cgarcia2097/8-Pack/case/views/OSH Park/Rev-1.2/Bottom.png

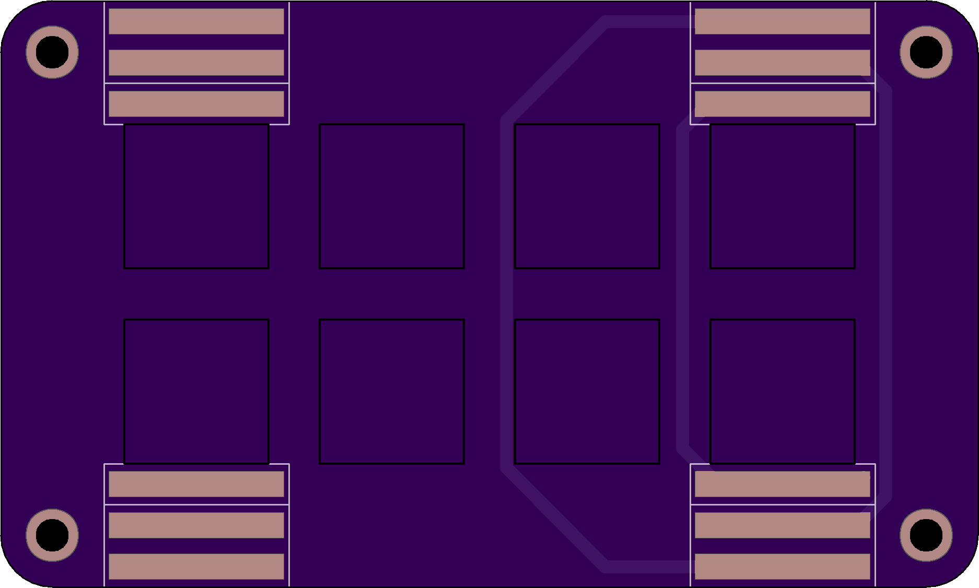
case/views/OSH Park/Rev-1.2/Bottom.png
