cgarcia2097/8-Pack/images/programming/getcode.PNG

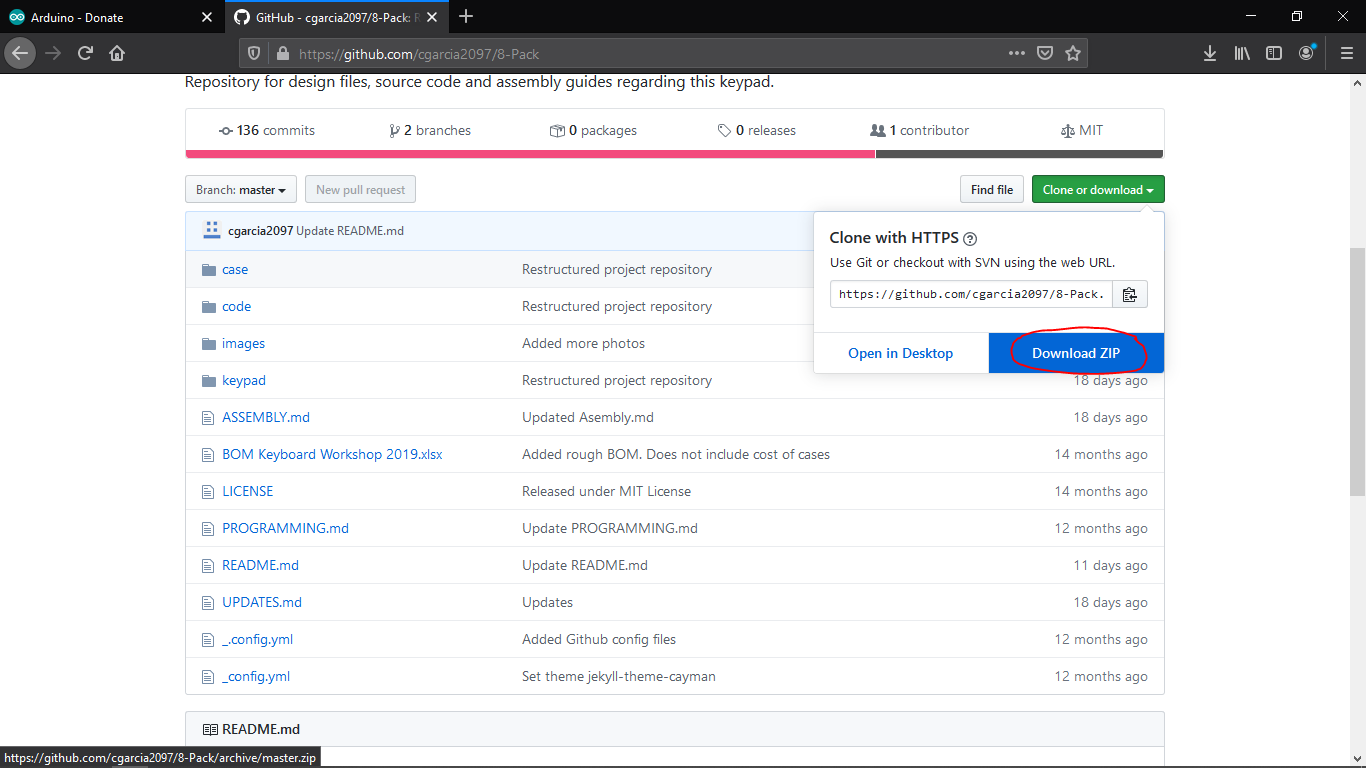
images/programming/getcode.PNG
