cgarcia2097/8-Pack/images/programming/gotolib.PNG

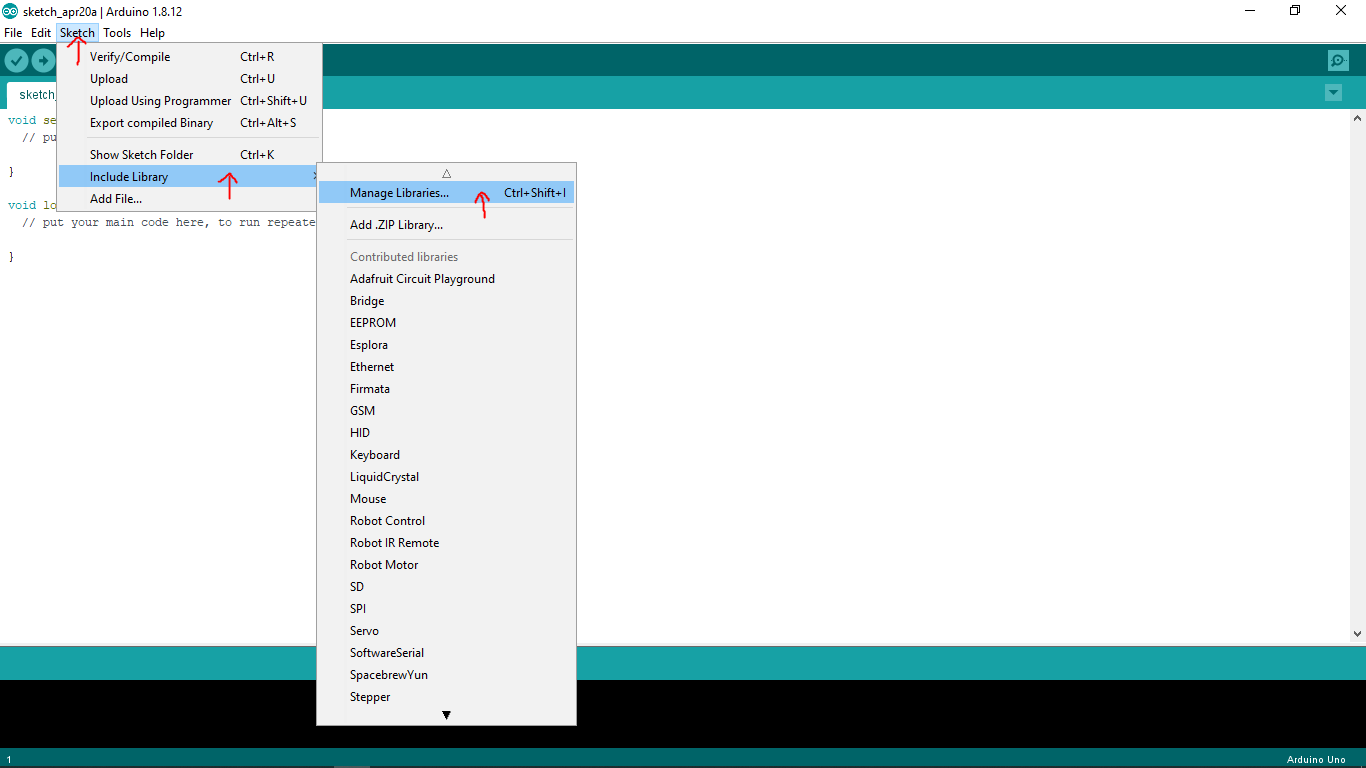
images/programming/gotolib.PNG
