cgarcia2097/8-Pack/keypad/8keysimple/views/KiCAD/back.png

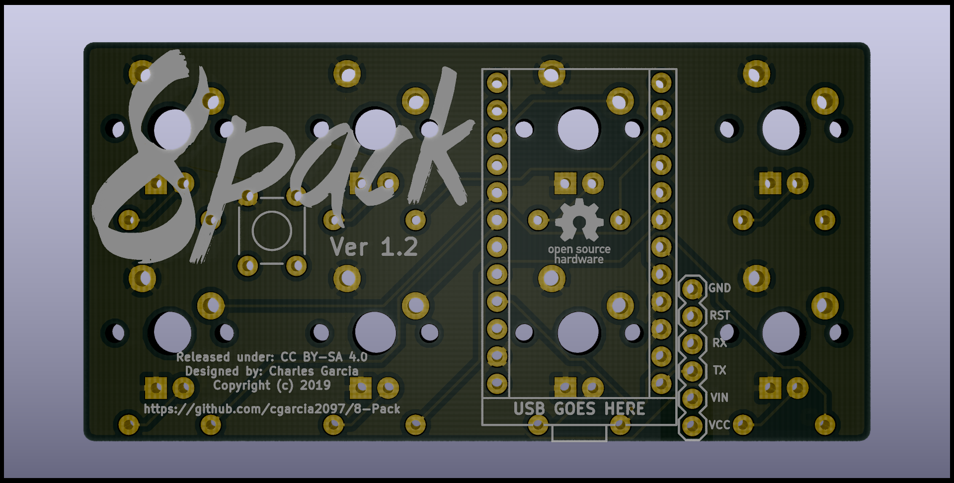
keypad/8keysimple/views/KiCAD/back.png
