cgarcia2097/8-Pack/keypad/8keysimple/views/KiCAD/front.png

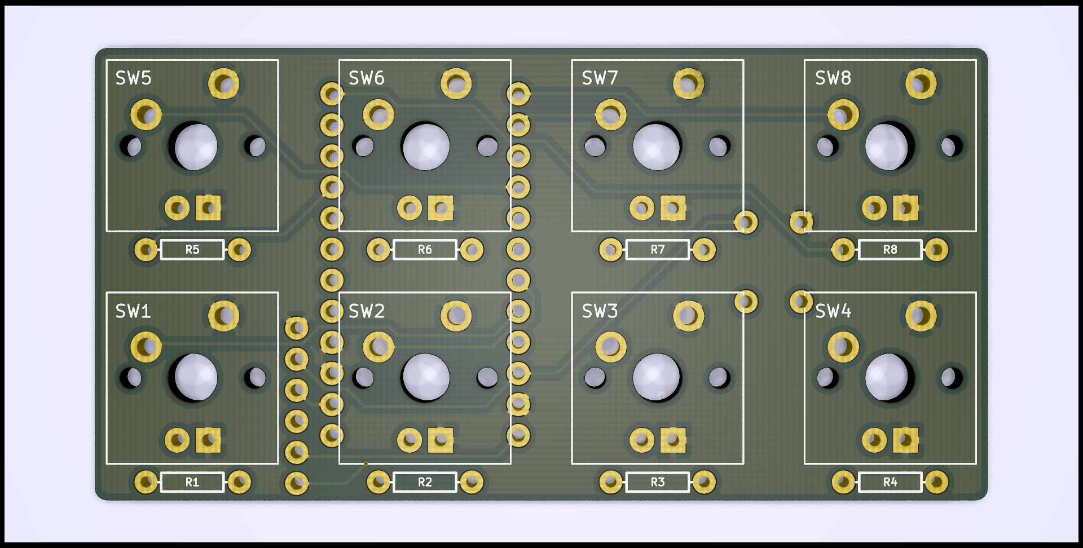
keypad/8keysimple/views/KiCAD/front.png
