cgarcia2097/8-Pack/keypad/8keysimple/views/OSH Park/1.2.1/back.png

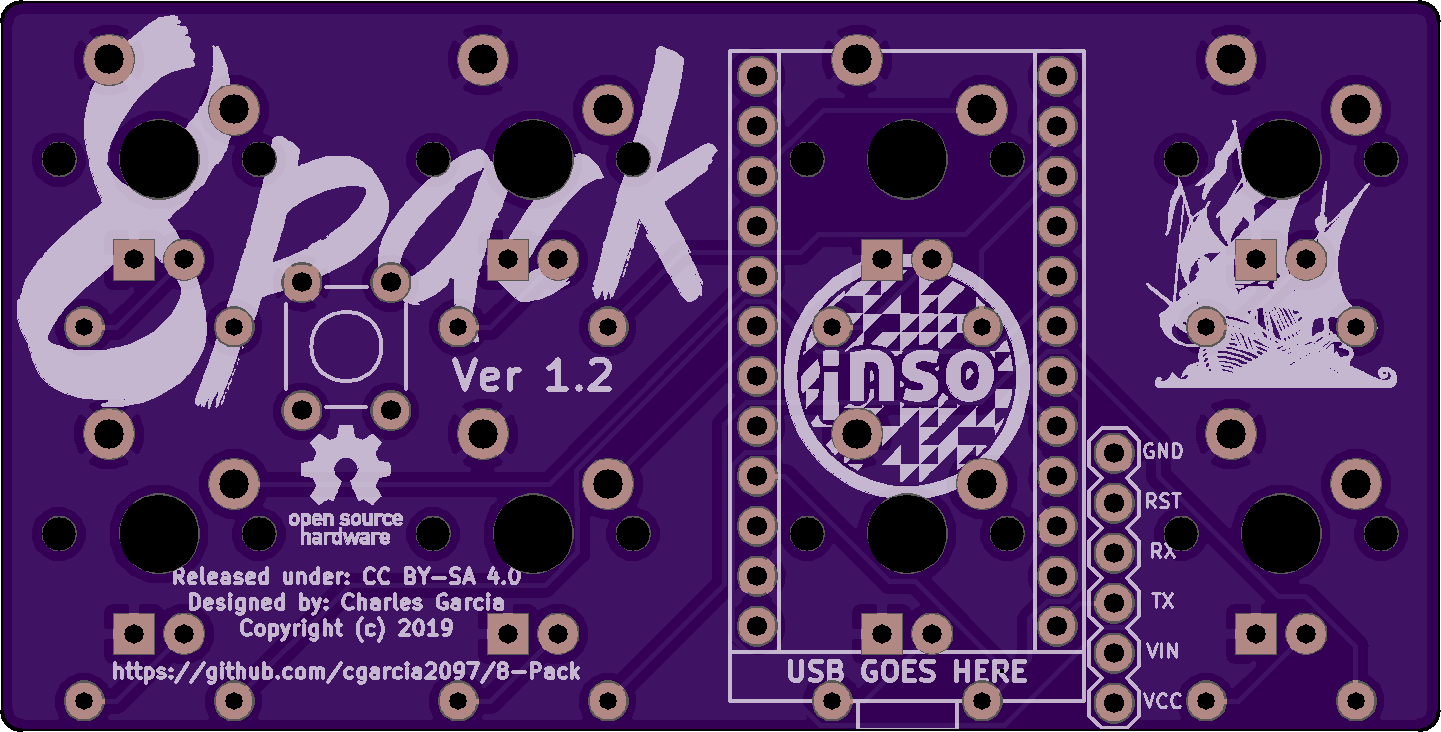
keypad/8keysimple/views/OSH Park/1.2.1/back.png
