cgarcia2097/8-Pack/keypad/8keysimple/views/x2/back.png

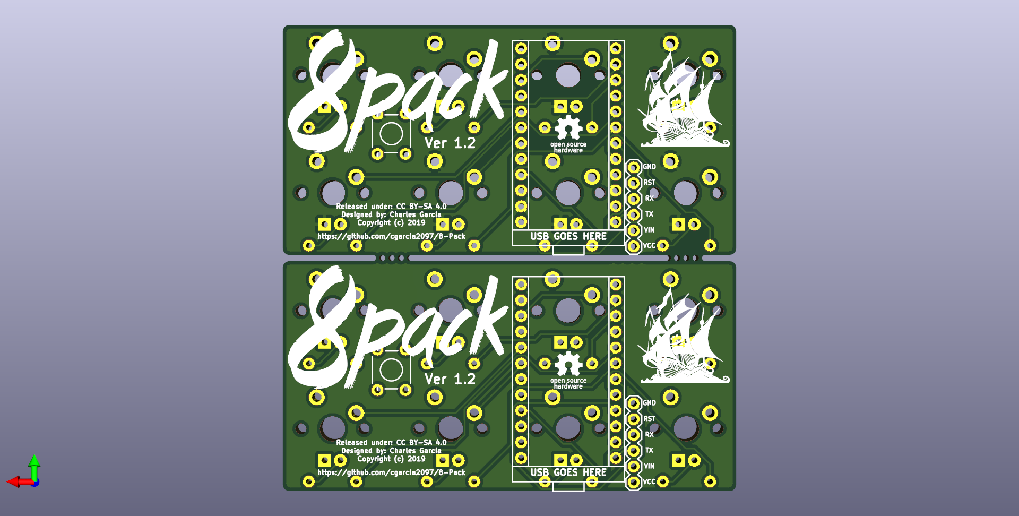
keypad/8keysimple/views/x2/back.png
