cgarcia2097/8-Pack/keypad/8keysimplev5/views/OSH Park/1.4.0/bottom.png

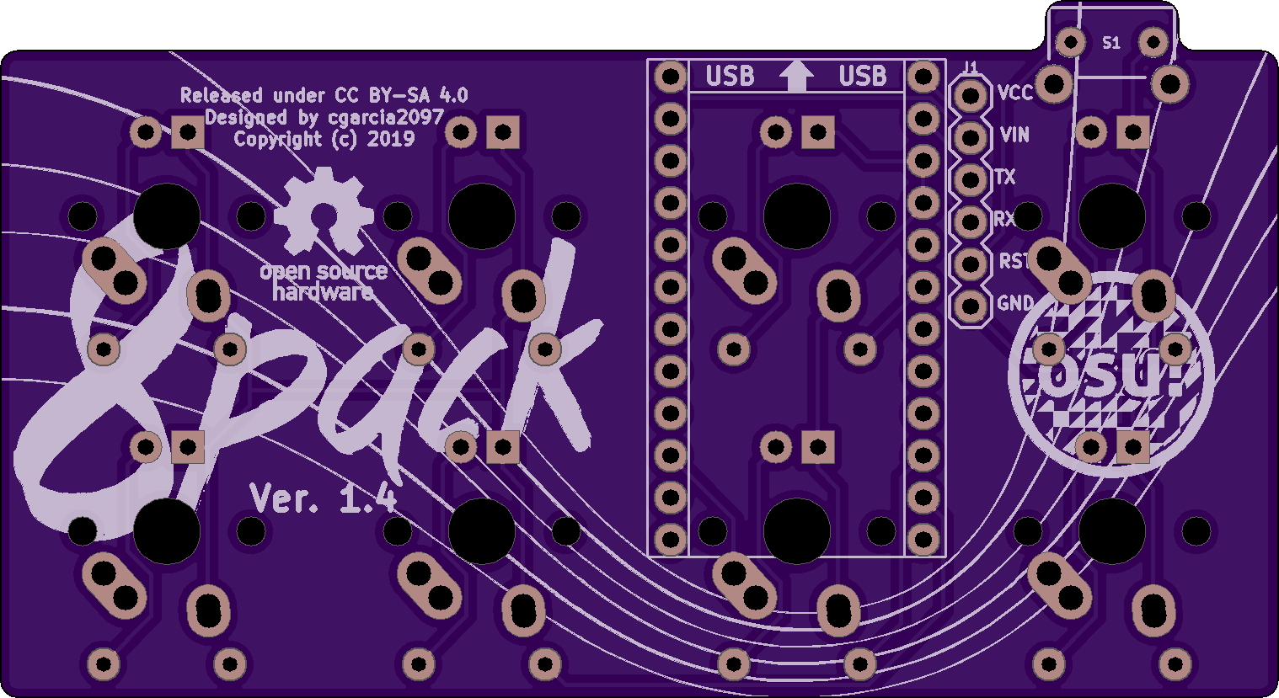
keypad/8keysimplev5/views/OSH Park/1.4.0/bottom.png
