cgarcia2097/8-Pack/keypad/8keysimplev6/views/OSH Park/pcb_osu_ontario_top.png

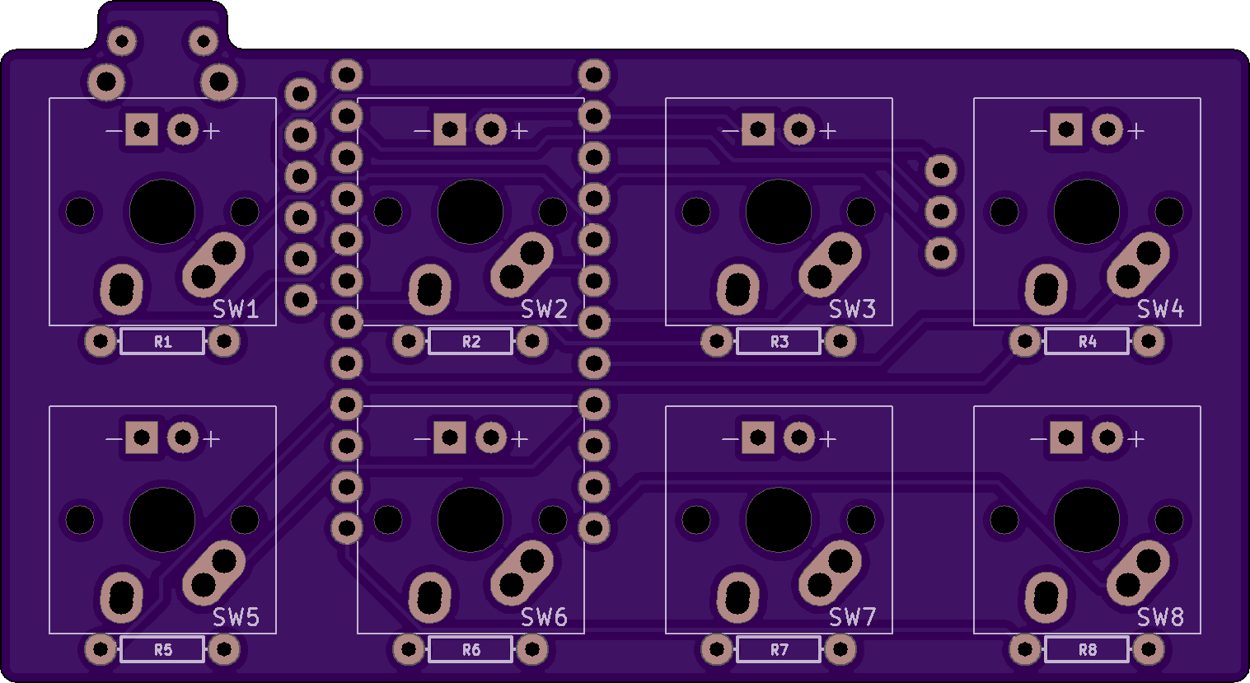
keypad/8keysimplev6/views/OSH Park/pcb_osu_ontario_top.png
