cgarcia2097/8-Pack/keypad/8keysimplev6/views/OSH Park/pcb_simple_bottom.png

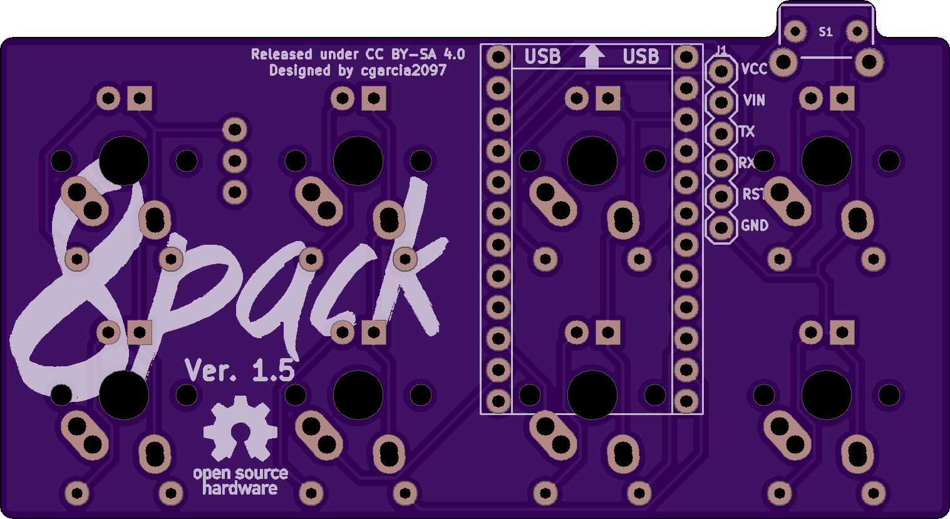
keypad/8keysimplev6/views/OSH Park/pcb_simple_bottom.png
