cgarcia2097/8-Pack/images/assembly/IMG_0136.JPG

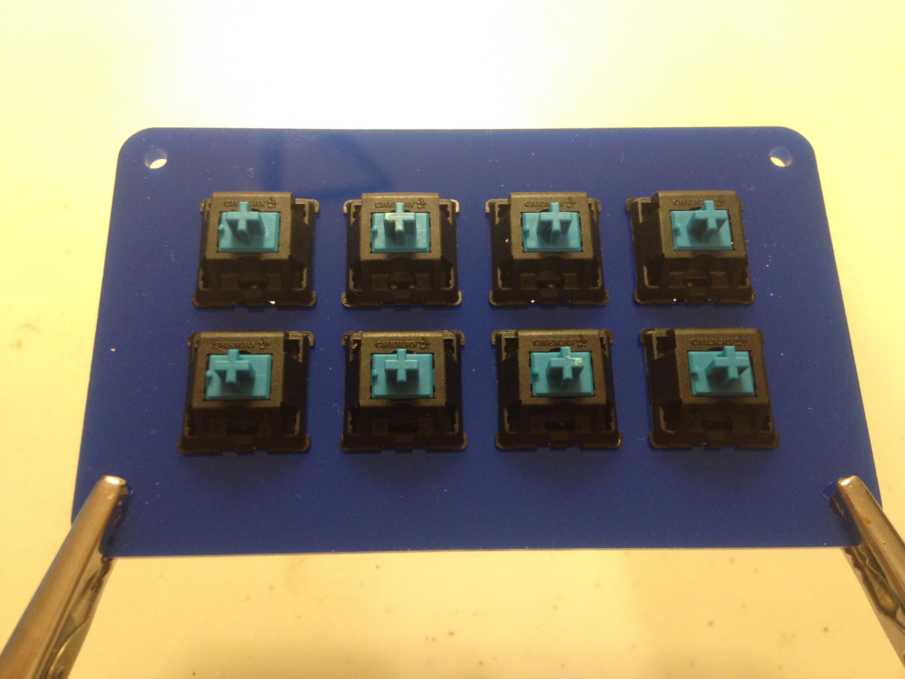
images/assembly/IMG_0136.JPG
