cgarcia2097/8-Pack/images/assembly/IMG_2523.JPG

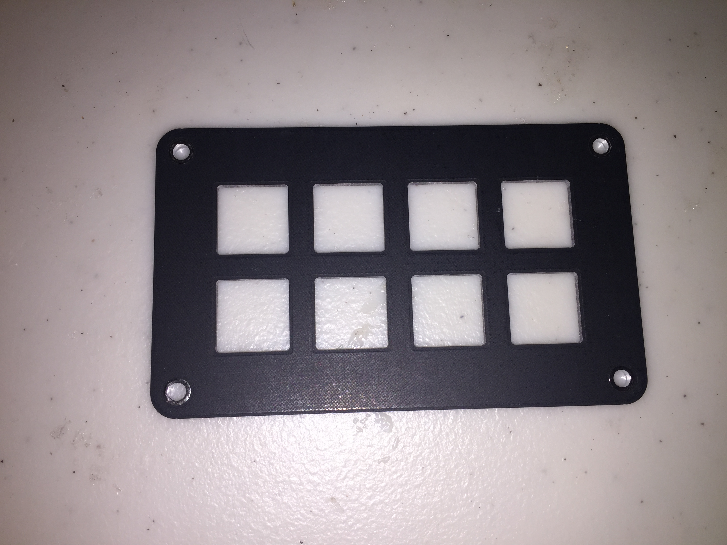
images/assembly/IMG_2523.JPG
