cgarcia2097/8-Pack/images/assembly/IMG_2525.JPG

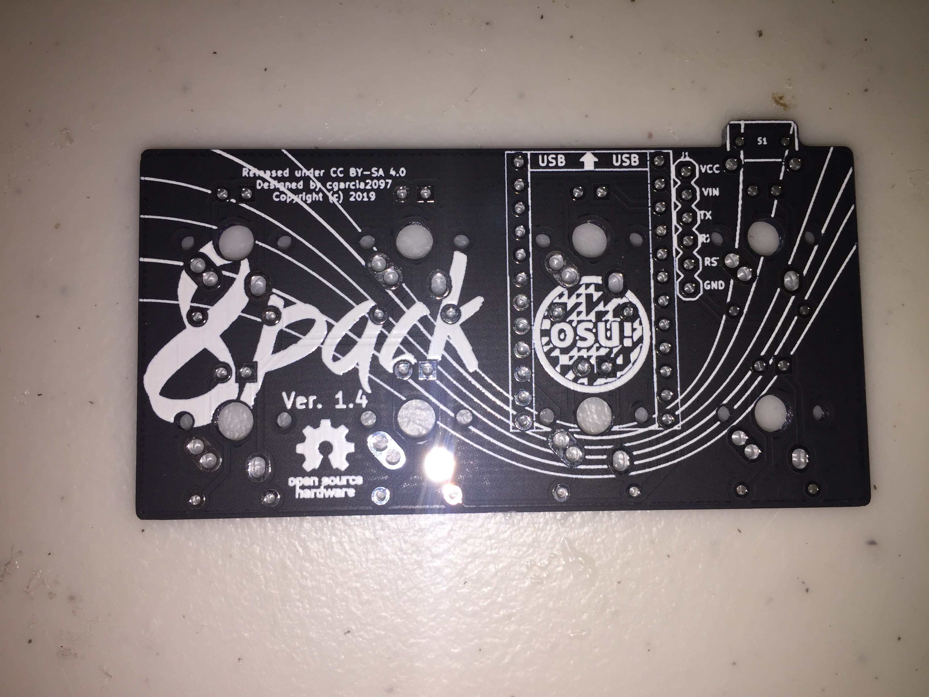
images/assembly/IMG_2525.JPG
