cgarcia2097/8-Pack/images/assembly/IMG_2526.JPG

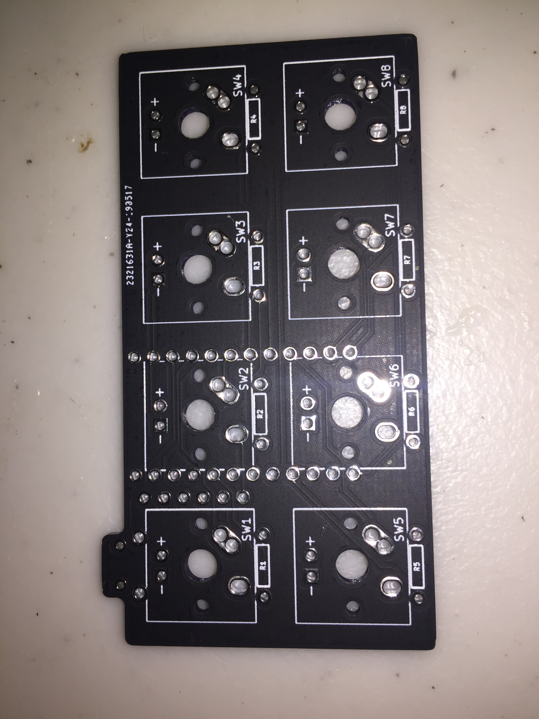
images/assembly/IMG_2526.JPG
