cgarcia2097/8-Pack/images/assembly/IMG_2527.JPG

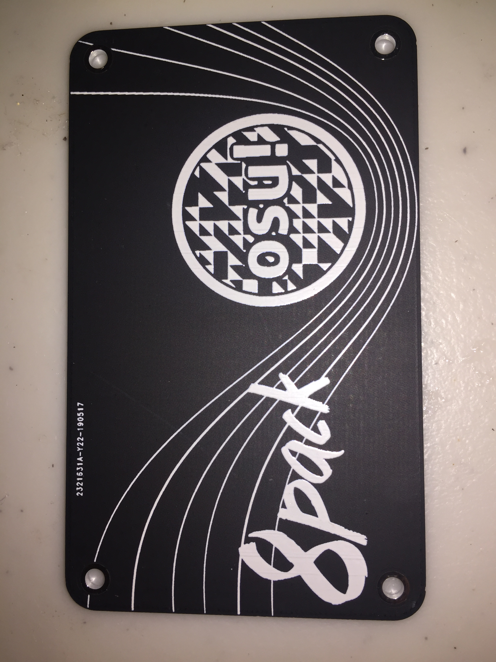
images/assembly/IMG_2527.JPG
