cgarcia2097/8-Pack/images/assembly/IMG_2528.JPG

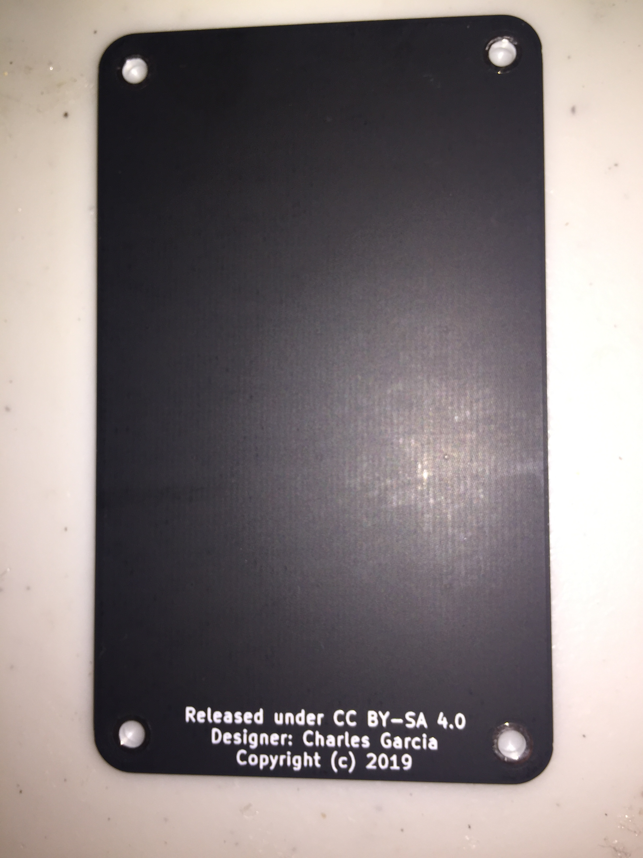
images/assembly/IMG_2528.JPG
