cgarcia2097/8-Pack/images/assembly/IMG_2530.JPG

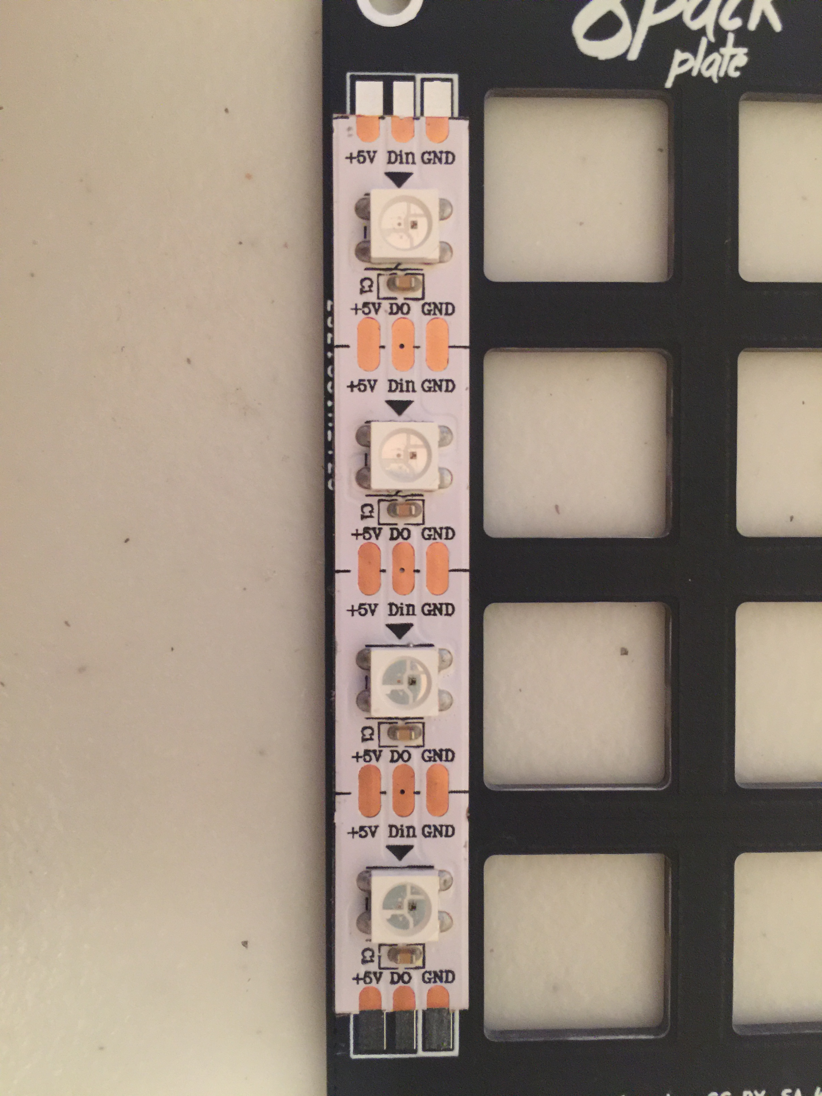
images/assembly/IMG_2530.JPG
