cgarcia2097/8-Pack/images/assembly/IMG_2539.JPG

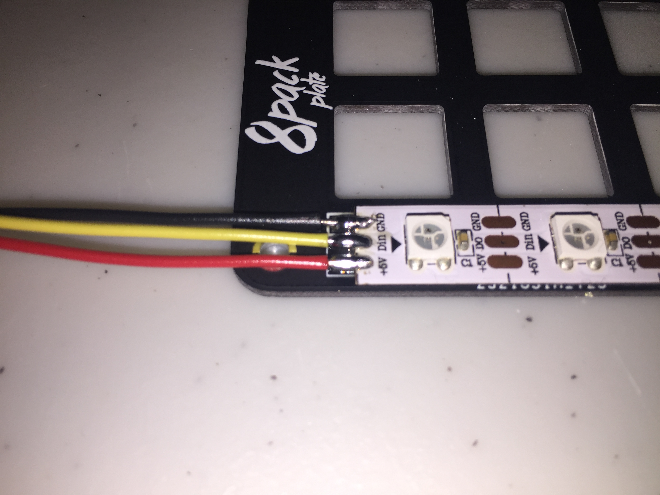
images/assembly/IMG_2539.JPG
