cgarcia2097/8-Pack/images/assembly/IMG_2540.JPG

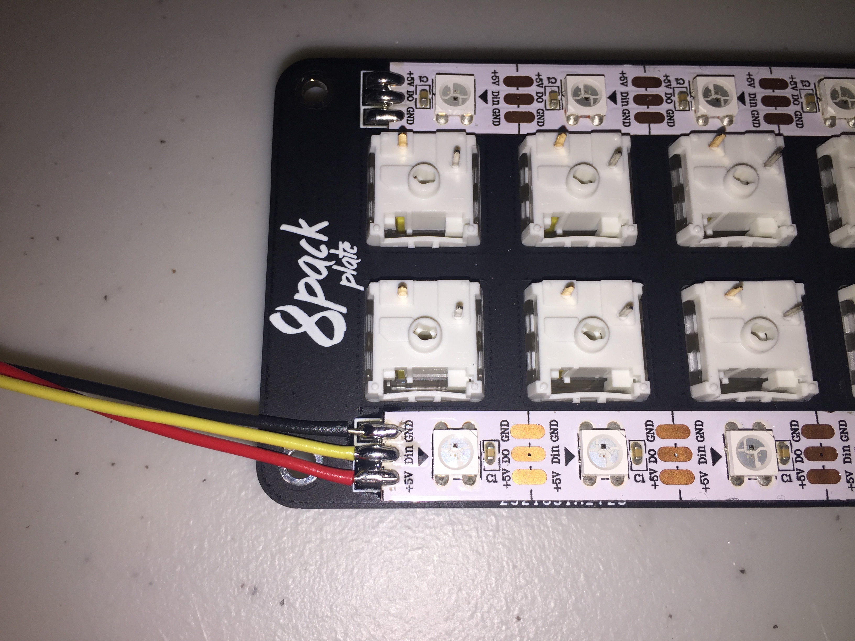
images/assembly/IMG_2540.JPG
