cgarcia2097/8-Pack/images/assembly/IMG_2545.JPG

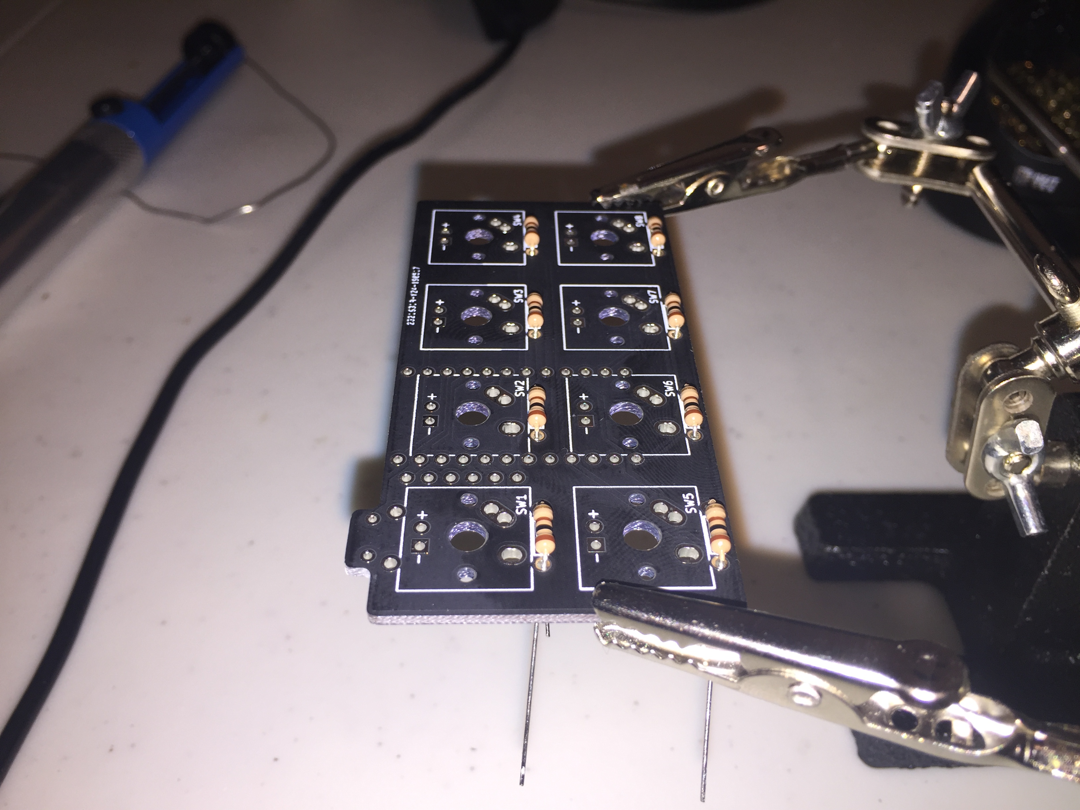
images/assembly/IMG_2545.JPG
