cgarcia2097/8-Pack/images/assembly/IMG_2547.JPG

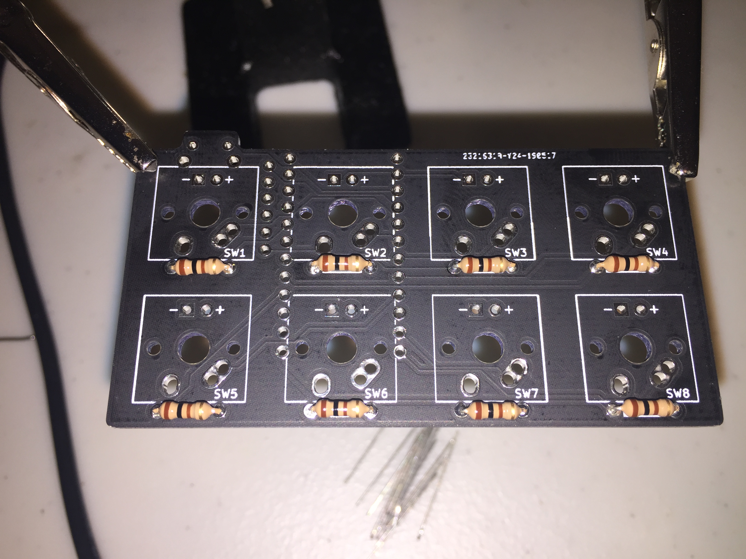
images/assembly/IMG_2547.JPG
