cgarcia2097/8-Pack/images/assembly/IMG_2552.JPG

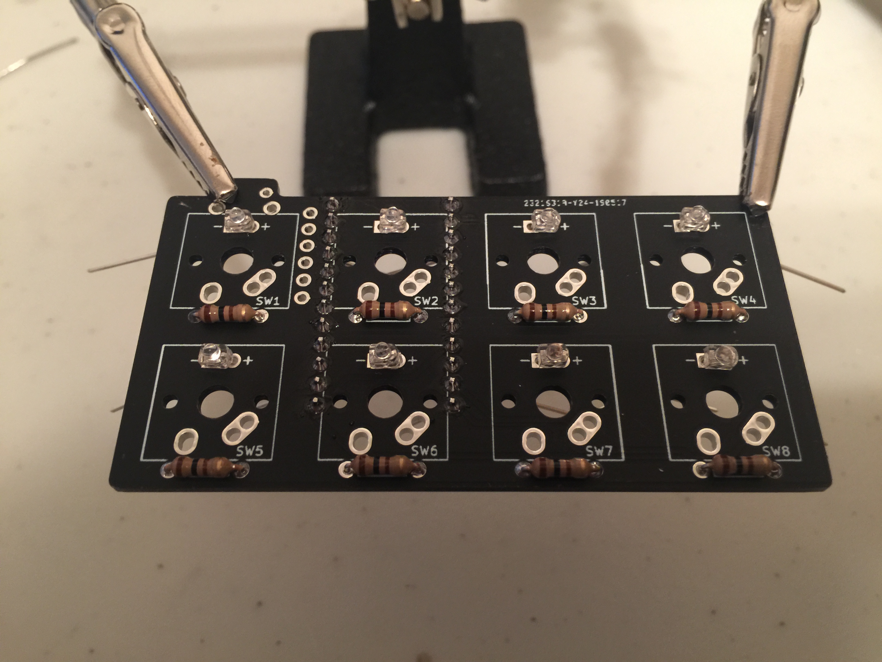
images/assembly/IMG_2552.JPG
