cgarcia2097/8-Pack/images/assembly/IMG_2553.JPG

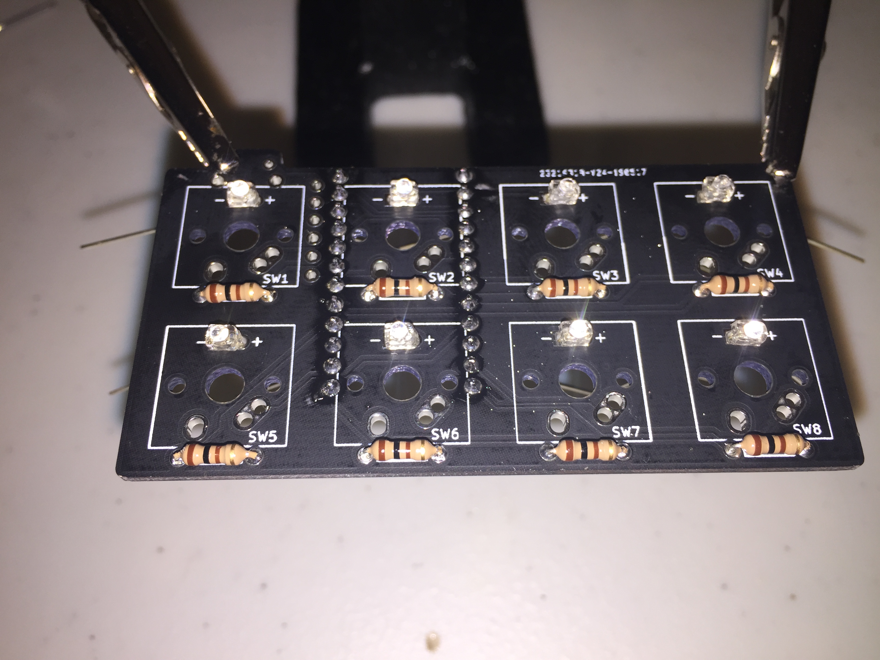
images/assembly/IMG_2553.JPG
