cgarcia2097/8-Pack/images/assembly/IMG_2554.JPG

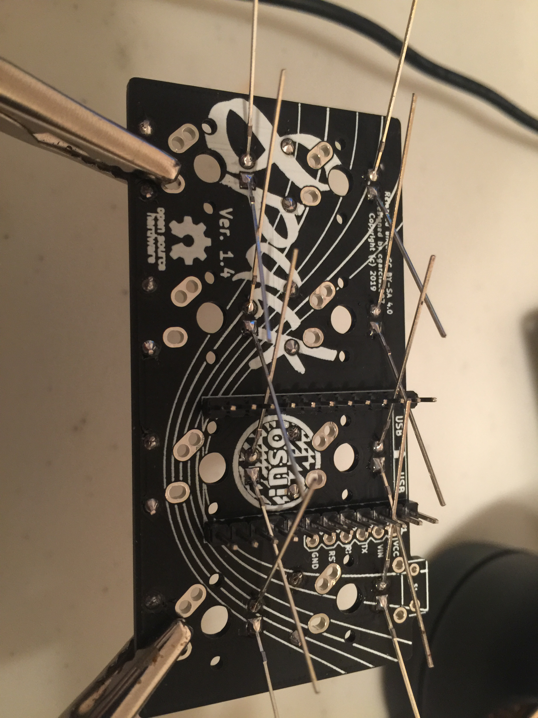
images/assembly/IMG_2554.JPG
