cgarcia2097/8-Pack/images/assembly/IMG_2555.JPG

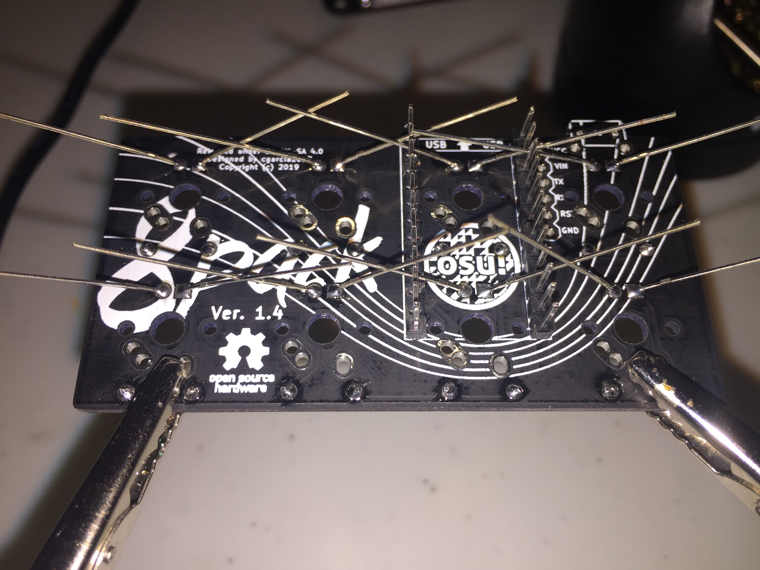
images/assembly/IMG_2555.JPG
