cgarcia2097/8-Pack/images/assembly/IMG_2556.JPG

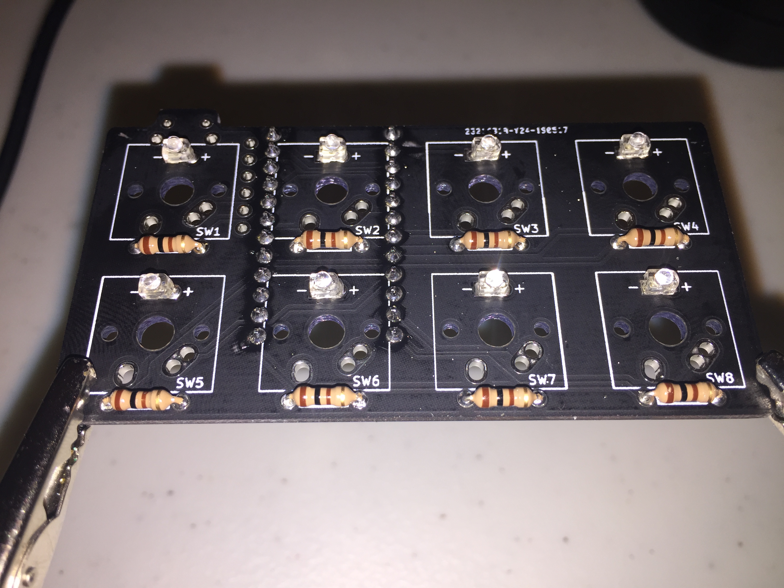
images/assembly/IMG_2556.JPG
