cgarcia2097/8-Pack/images/assembly/IMG_2559.JPG

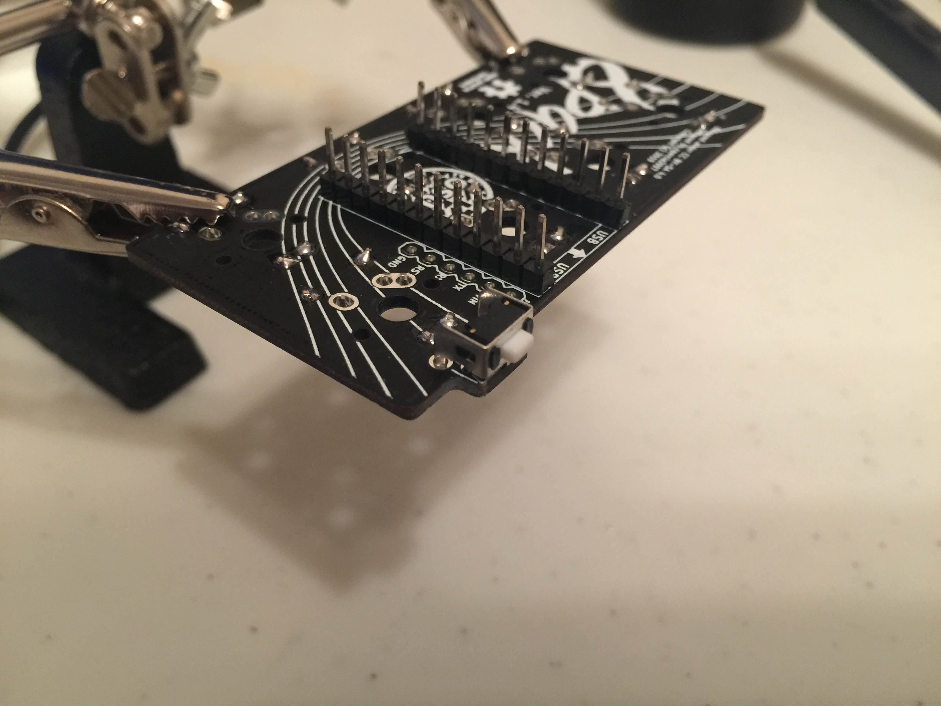
images/assembly/IMG_2559.JPG
