cgarcia2097/8-Pack/images/assembly/IMG_2568.JPG

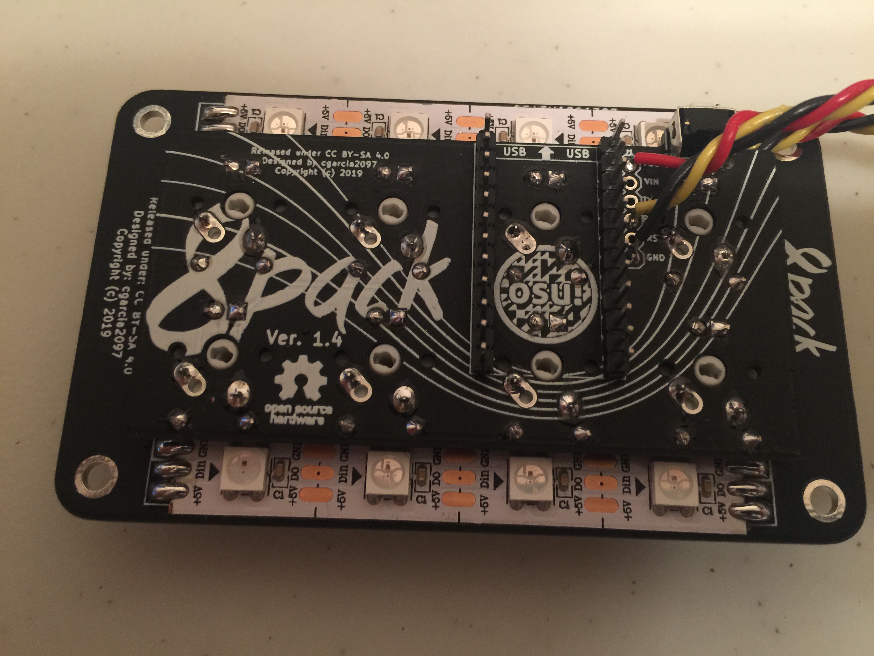
images/assembly/IMG_2568.JPG
