cgarcia2097/8-Pack/images/assembly/IMG_2570.JPG

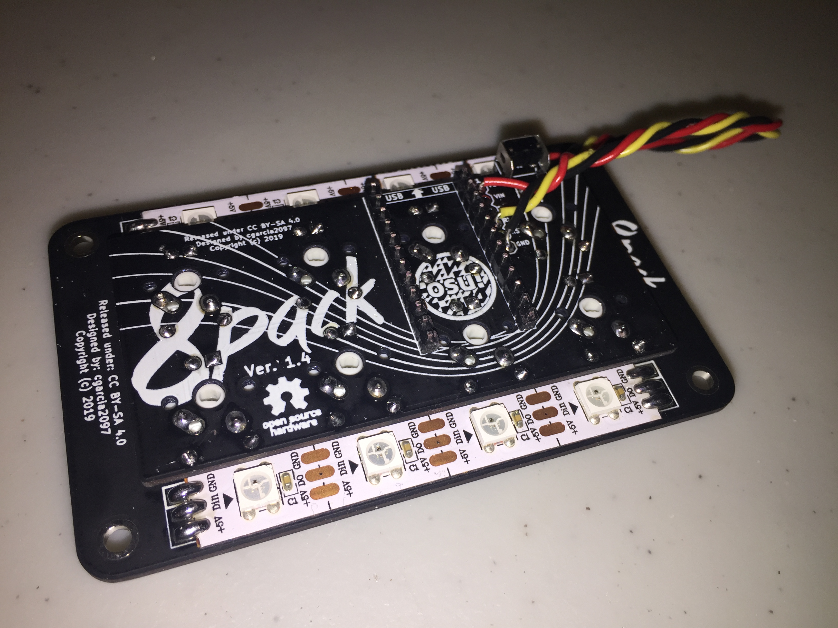
images/assembly/IMG_2570.JPG
