cgarcia2097/8-Pack/images/assembly/IMG_2571.JPG

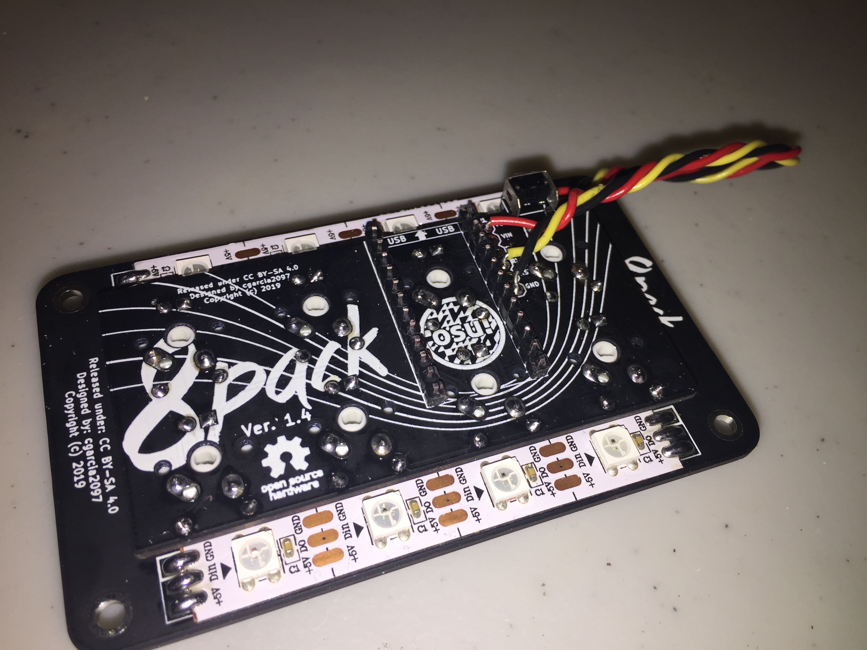
images/assembly/IMG_2571.JPG
