cgarcia2097/8-Pack/images/assembly/IMG_2572.JPG

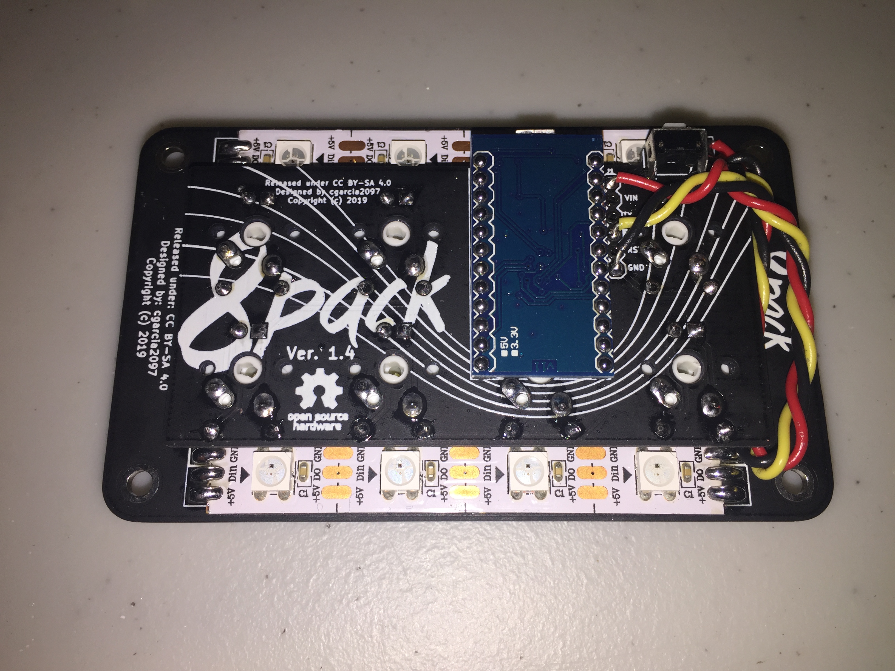
images/assembly/IMG_2572.JPG
