cgarcia2097/8-Pack/images/assembly/IMG_2574.JPG

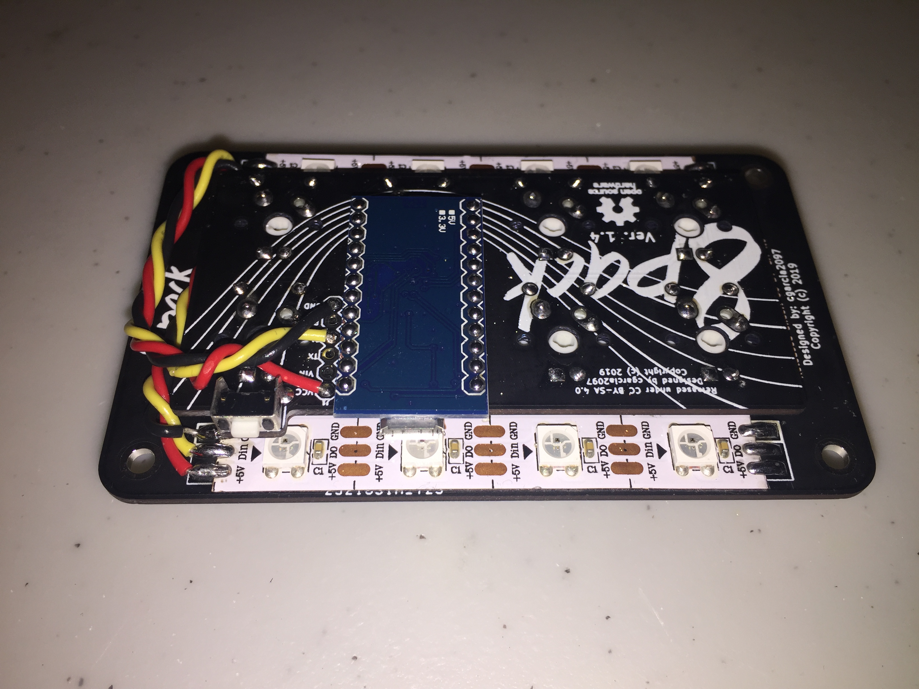
images/assembly/IMG_2574.JPG
