cgarcia2097/8-Pack/images/assembly/IMG_2576.JPG

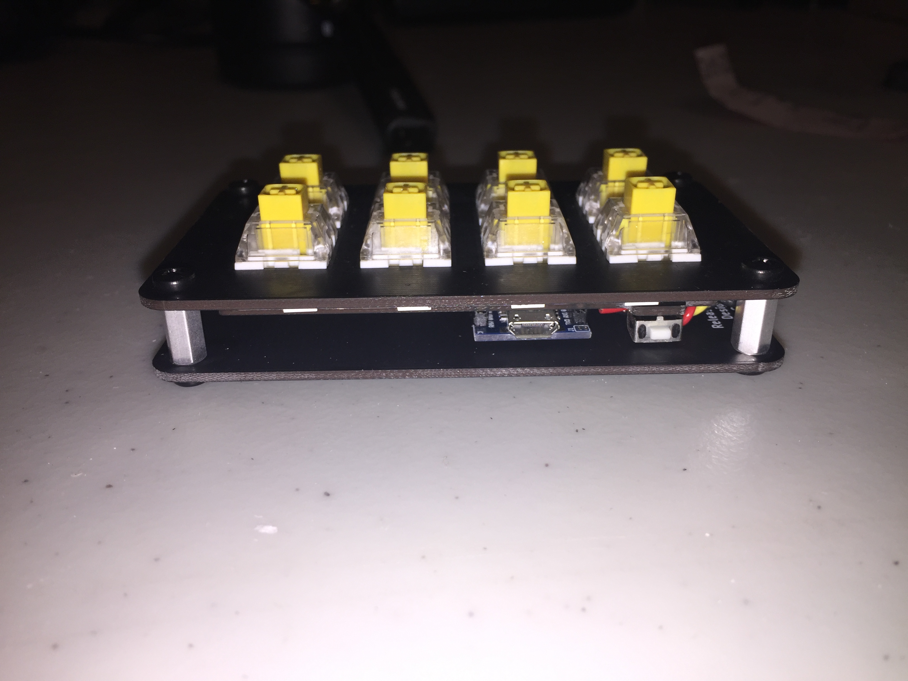
images/assembly/IMG_2576.JPG
