cgarcia2097/8-Pack/images/assembly/IMG_2578.JPG

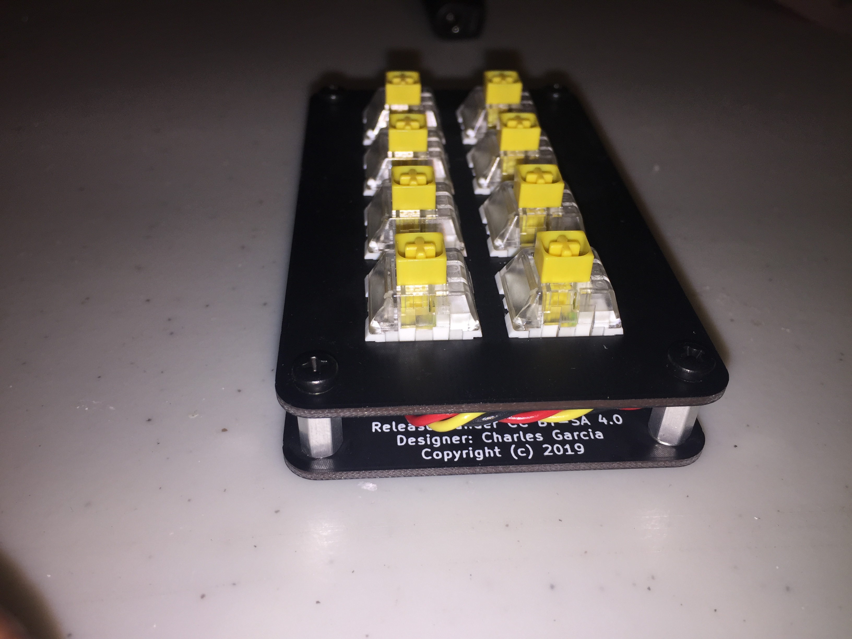
images/assembly/IMG_2578.JPG
