cgarcia2097/8-Pack/images/assembly/IMG_2579.JPG

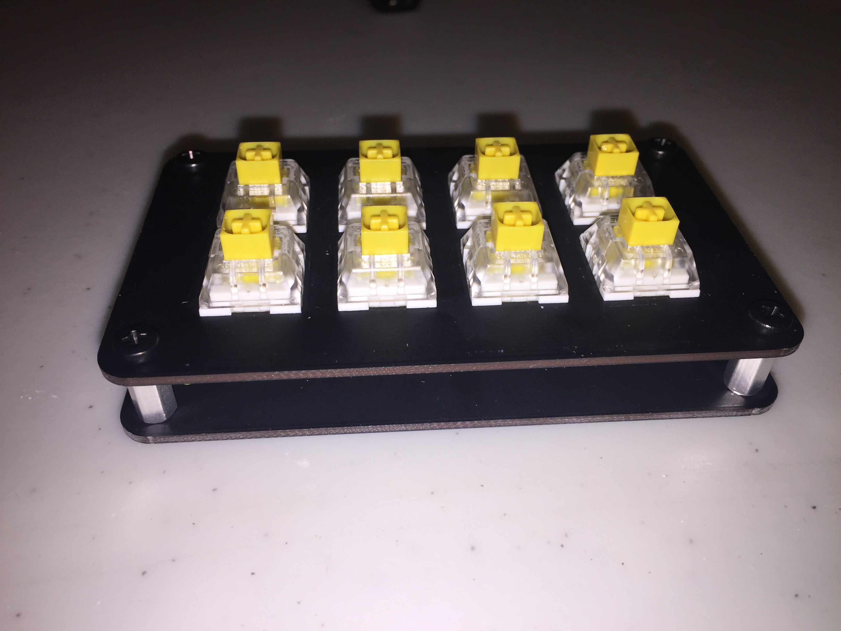
images/assembly/IMG_2579.JPG
