cgarcia2097/8-Pack/images/assembly/IMG_2580.JPG

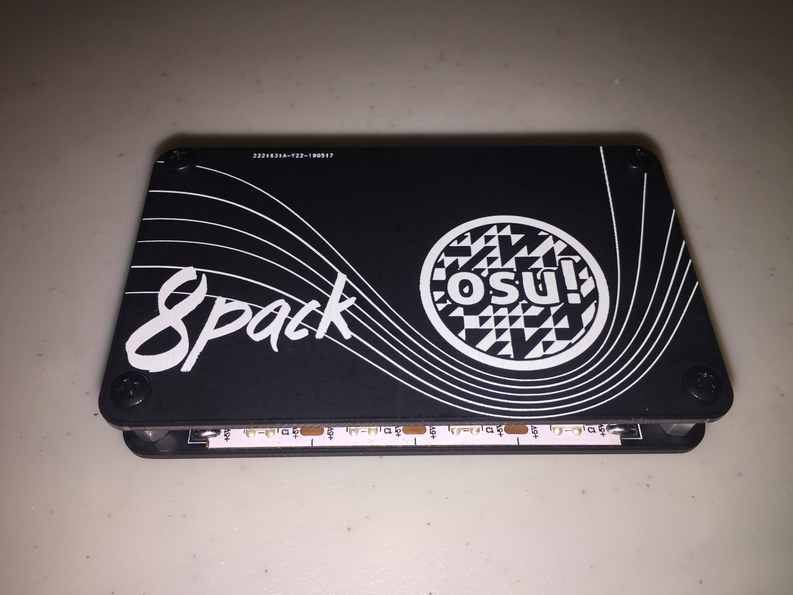
images/assembly/IMG_2580.JPG
